TimothyThompkins/InteractiveGame/Fuse Settings/Low Fuse BIts Atmega328p.png

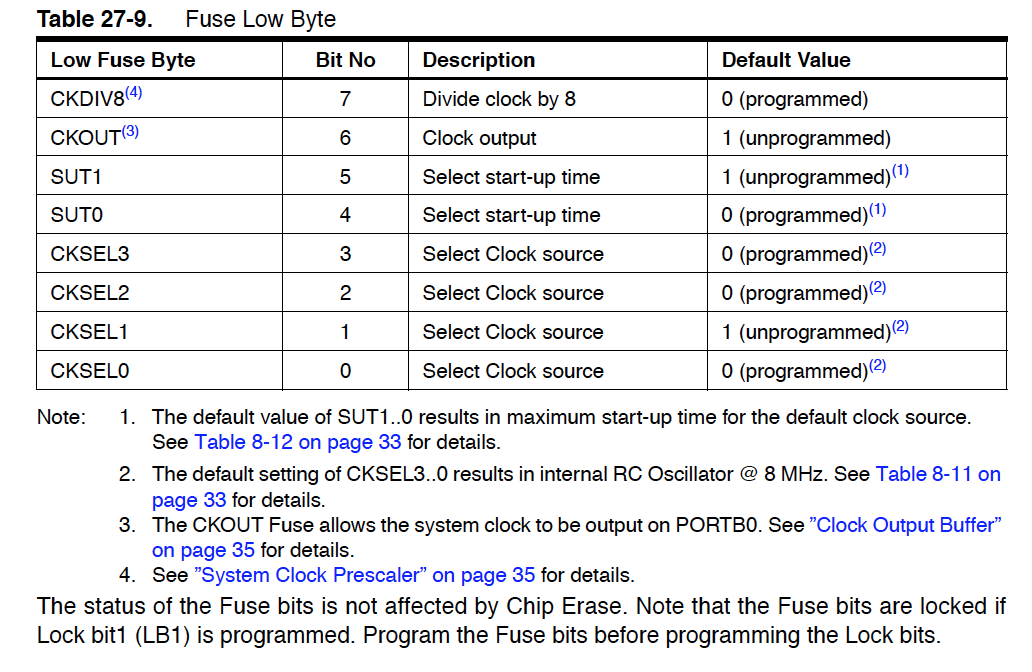
Fuse Settings/Low Fuse BIts Atmega328p.png
