TimothyThompkins/InteractiveGame/Game/python/characters/Fighter.gif

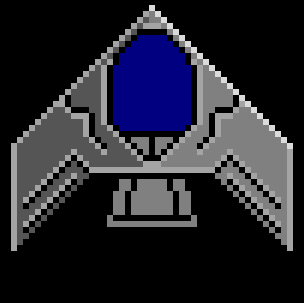
Game/python/characters/Fighter.gif
