TimothyThompkins/InteractiveGame/Game/python/serial_comms.py

import sys
import glob
import serial
#import time

baudrates = [110, 300, 600, 1200, 2400, 4800, 9600, 14400, 19200, 28800, 38400, 56000, 57600, 115200]
error_msg = "Error: No Serial ports available"

class serial_comms():

    def __init__(self, serial_port, baud_rate):

        self.port = serial_port
        self.baudrate = baud_rate
        self.stopbits = serial.STOPBITS_ONE # Changed from two
        self.bytesize = serial.EIGHTBITS

        self._open_serial_port()

    # Open the serial port with these parameters
    def _open_serial_port(self):

        self.ser = serial.Serial(
            port = self.port,
            baudrate = self.baudrate,
            stopbits = serial.STOPBITS_TWO,
            bytesize = serial.EIGHTBITS,
        )

        self.ser.isOpen()

    # TMT This needs work, these are just placeholders
    def send_data(self, data):
        # delim = bytes([])
        # ser.write(data+delim)
        self.ser.write(data)

    def recv_data(self):
        self.ser.isOpen()
        delim = "\x00"
        recvd = "".join(iter(lambda:ser.read(1),delim))
        return recvd

    def _a2s(arr):
        """ Array of integer byte values --> binary string
        """
        return ''.join(chr(b) for b in arr)

    #def test_comms(self):


def get_port_options(system):
    """Lists serial ports

    :raises EnvironmentError:
        On unsupported or unknown platforms
    :returns:
        A list of available serial ports
    """
    sys_platform = system.get_sys_platform()

    # For Windows Platform
    if sys_platform == 'windows':
        ports = ['COM' + str(i + 1) for i in range(256)]

    # For Linux Platforms
    elif sys_platform == 'linux':
        # this is to exclude your current terminal "/dev/tty"
        ports = glob.glob('/dev/tty[A-Za-z]*')
        result_test = []

        for a_port in ports:
            try:
                s = serial.Serial(a_port)
                s.close()
                result_test.append(a_port)
            except serial.SerialException:
                pass

        print (result_test)
        # return result

    # For OSX Platforms
    elif sys_platform == 'OSX':
        ports = glob.glob('/dev/tty.*')

    else:
        raise EnvironmentError('Unsupported platform')

    result = []
    for port in ports:
        try:
            s = serial.Serial(port)
            s.close()
            result.append(port)
        except (OSError, serial.SerialException):
            pass

    if len(result) == 0:
        result.append(error_msg)

    return result

def get_baud_options():
    return baudrates
